ecoagrotec/papatronica/firmware/mpu6050esp32.ino

#include <Wire.h>
#include "BluetoothSerial.h"

// MPU6050 Slave Device Address
const uint8_t MPU6050SlaveAddress = 0x68;

// Select SDA and SCL pins for I2C communication 
const uint8_t scl = 16;
const uint8_t sda = 17;

// sensitivity scale factor respective to full scale setting provided in datasheet 
//const uint16_t AccelScaleFactor = 16384;
const uint16_t AccelScaleFactor = 8192;
const uint16_t GyroScaleFactor = 131;

// MPU6050 few configuration register addresses
const uint8_t MPU6050_REGISTER_SMPLRT_DIV   =  0x19;
const uint8_t MPU6050_REGISTER_USER_CTRL    =  0x6A;
const uint8_t MPU6050_REGISTER_PWR_MGMT_1   =  0x6B;
const uint8_t MPU6050_REGISTER_PWR_MGMT_2   =  0x6C;
const uint8_t MPU6050_REGISTER_CONFIG       =  0x1A;
const uint8_t MPU6050_REGISTER_GYRO_CONFIG  =  0x1B;
const uint8_t MPU6050_REGISTER_ACCEL_CONFIG =  0x1C;
const uint8_t MPU6050_REGISTER_FIFO_EN      =  0x23;
const uint8_t MPU6050_REGISTER_INT_ENABLE   =  0x38;
const uint8_t MPU6050_REGISTER_ACCEL_XOUT_H =  0x3B;
const uint8_t MPU6050_REGISTER_SIGNAL_PATH_RESET  = 0x68;

int16_t AccelX, AccelY, AccelZ, Temperature, GyroX, GyroY, GyroZ;

#if !defined(CONFIG_BT_ENABLED) || !defined(CONFIG_BLUEDROID_ENABLED)
#error Bluetooth is not enabled! Please run `make menuconfig` to and enable it
#endif

BluetoothSerial SerialBT;


void setup() 
{
  Serial.begin(9600);
  Wire.begin(sda, scl);
  MPU6050_Init();

  SerialBT.begin("PAPATRONICA"); //Bluetooth device name
  Serial.println("The device started, now you can pair it with bluetooth!");


}

char buf_acc[100];
char buf_tmp[10];

void loop() 
{
  double Ax, Ay, Az, T, Gx, Gy, Gz;
  
  Read_RawValue(MPU6050SlaveAddress, MPU6050_REGISTER_ACCEL_XOUT_H);
  
  //divide each with their sensitivity scale factor
  Ax = (double)AccelX/AccelScaleFactor;
  Ay = (double)AccelY/AccelScaleFactor;
  Az = (double)AccelZ/AccelScaleFactor;
  T = (double)Temperature/340+36.53; //temperature formula
  Gx = (double)GyroX/GyroScaleFactor;
  Gy = (double)GyroY/GyroScaleFactor;
  Gz = (double)GyroZ/GyroScaleFactor;

  /*
  Serial.print("Ax: "); Serial.print(Ax);
  Serial.print(" Ay: "); Serial.print(Ay);
  Serial.print(" Az: "); Serial.print(Az);
  Serial.print(" T: "); Serial.print(T);
  Serial.print(" Gx: "); Serial.print(Gx);
  Serial.print(" Gy: "); Serial.print(Gy);
  Serial.print(" Gz: "); Serial.println(Gz);
  */
  
  strcpy(buf_acc,"*Ax:"); sprintf(buf_tmp,"%2.2f",Ax); strcat(buf_acc,buf_tmp);
  strcat(buf_acc," Ay:"); sprintf(buf_tmp,"%2.2f",Ay); strcat(buf_acc,buf_tmp);
  strcat(buf_acc," Az:"); sprintf(buf_tmp,"%2.2f",Az); strcat(buf_acc,buf_tmp);
  strcat(buf_acc," Tp:"); sprintf(buf_tmp,"%2.2f",T); strcat(buf_acc,buf_tmp);
  strcat(buf_acc,"*\r\n");

  
  //if (Serial.available()) 
  if (1)
  {
    SerialBT.write((uint8_t *)buf_acc,sizeof(buf_acc));
  }
  
  if (SerialBT.available()) 
  {
    Serial.write(SerialBT.read());
  }
    
  delay(500);

  
}

void I2C_Write(uint8_t deviceAddress, uint8_t regAddress, uint8_t data){
  Wire.beginTransmission(deviceAddress);
  Wire.write(regAddress);
  Wire.write(data);
  Wire.endTransmission();
}

// read all 14 register
void Read_RawValue(uint8_t deviceAddress, uint8_t regAddress){
  Wire.beginTransmission(deviceAddress);
  Wire.write(regAddress);
  Wire.endTransmission();
  Wire.requestFrom(deviceAddress, (uint8_t)14);
  AccelX = (((int16_t)Wire.read()<<8) | Wire.read());
  AccelY = (((int16_t)Wire.read()<<8) | Wire.read());
  AccelZ = (((int16_t)Wire.read()<<8) | Wire.read());
  Temperature = (((int16_t)Wire.read()<<8) | Wire.read());
  GyroX = (((int16_t)Wire.read()<<8) | Wire.read());
  GyroY = (((int16_t)Wire.read()<<8) | Wire.read());
  GyroZ = (((int16_t)Wire.read()<<8) | Wire.read());
}

//configure MPU6050
void MPU6050_Init(){
  delay(150);
  I2C_Write(MPU6050SlaveAddress, MPU6050_REGISTER_SMPLRT_DIV, 0x07);
  I2C_Write(MPU6050SlaveAddress, MPU6050_REGISTER_PWR_MGMT_1, 0x01);
  I2C_Write(MPU6050SlaveAddress, MPU6050_REGISTER_PWR_MGMT_2, 0x00);
  I2C_Write(MPU6050SlaveAddress, MPU6050_REGISTER_CONFIG, 0x00);
  I2C_Write(MPU6050SlaveAddress, MPU6050_REGISTER_GYRO_CONFIG, 0x00);//set +/-250 degree/second full scale
  I2C_Write(MPU6050SlaveAddress, MPU6050_REGISTER_ACCEL_CONFIG, 0x08);// set +/- 2g full scale
  I2C_Write(MPU6050SlaveAddress, MPU6050_REGISTER_FIFO_EN, 0x00);
  I2C_Write(MPU6050SlaveAddress, MPU6050_REGISTER_INT_ENABLE, 0x01);
  I2C_Write(MPU6050SlaveAddress, MPU6050_REGISTER_SIGNAL_PATH_RESET, 0x00);
  I2C_Write(MPU6050SlaveAddress, MPU6050_REGISTER_USER_CTRL, 0x00);
}
